jesco-t/onstep-whc/include/Common.h

#pragma once

/*
 * DEFINITIONS FOR TASK SCHEDULER
 */
#define _TASK_SLEEP_ON_IDLE_RUN // Enable 1 ms SLEEP_IDLE powerdowns between tasks if no callback methods were invoked during the pass
#define _TASK_STATUS_REQUEST    // Compile with support for StatusRequest functionality - triggering tasks on status change events in addition to time only
// #define _TASK_WDT_IDS           // Compile with support for wdt control points and task ids
// #define _TASK_PRIORITY          // Support for layered scheduling priority
// #define _TASK_STD_FUNCTION      // Support for std::function (ESP8266 and ESP32 ONLY)

/*
 * DEBUGGING via SERIAL MONITOR
 */
#define DebugSer Serial

#ifdef DEBUG
  #define D(x)       DebugSer.print(x)
  #define DF(x)      DebugSer.print(F(x))
  #define DL(x)      DebugSer.println(x)
  #define DLF(x)     DebugSer.println(F(x))
#else
  #define D(x)
  #define DF(x)
  #define DL(x)
  #define DLF(x)
#endif

/*
 * INCLUDES
 */
#include <Arduino.h>
#include <ESP8266WiFi.h>
#include <WiFiClient.h>
#include <Wire.h>
#include <Adafruit_GFX.h>
#include <Adafruit_SSD1306.h>
#include <TaskScheduler.h>
